codepainters/e800j/docs/scans/cpu800j1.gif

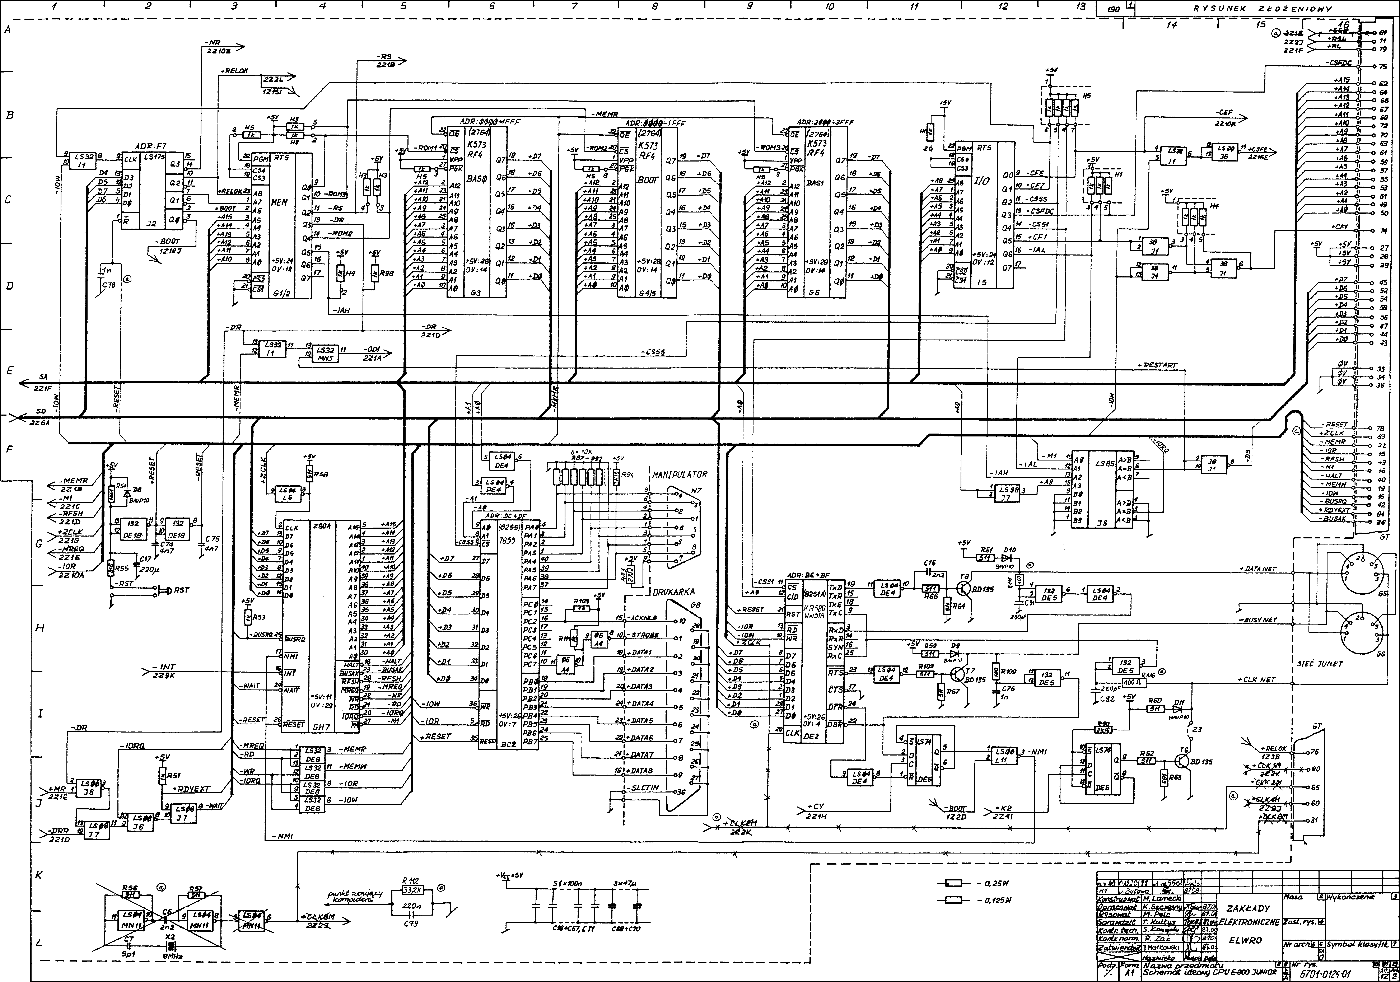
docs/scans/cpu800j1.gif
