codepainters/e800j/docs/scart/1.3_cvbs.jpg

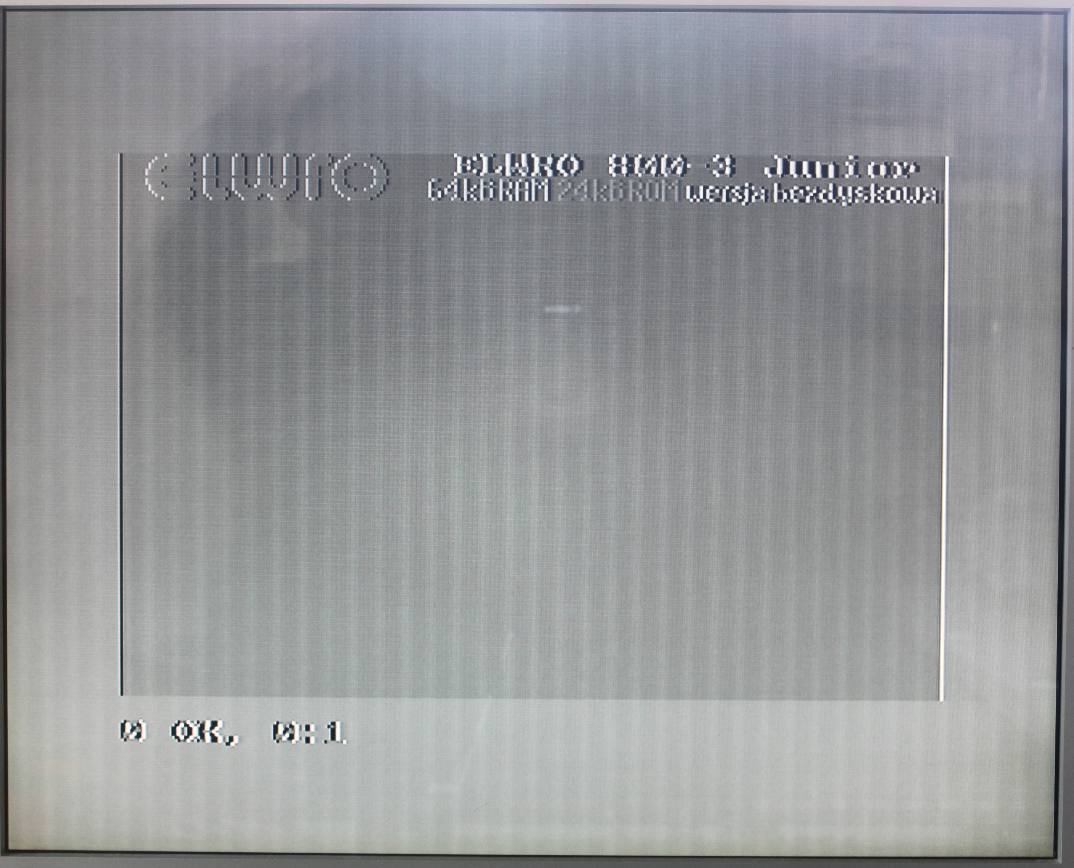
docs/scart/1.3_cvbs.jpg
