codepainters/e800j/docs/scart/scope/p16_b7.png

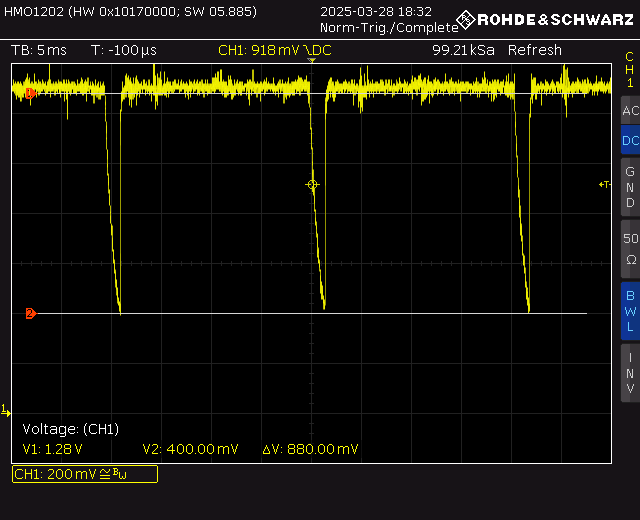
docs/scart/scope/p16_b7.png
