codepainters/e800j/docs/scart/scope/sync_loaded_noise.png

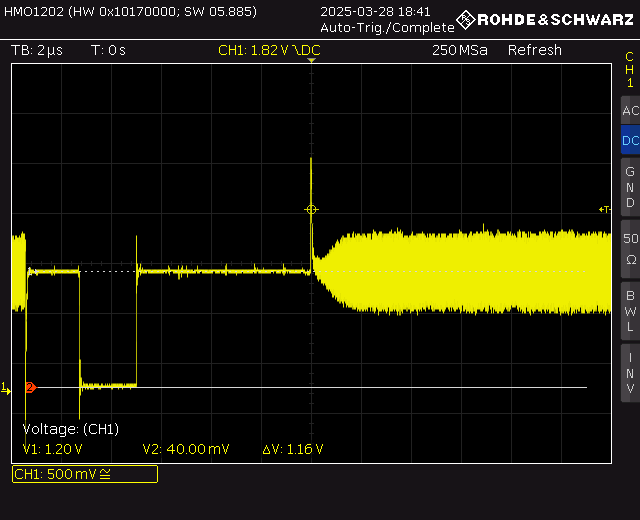
docs/scart/scope/sync_loaded_noise.png
