codepainters/e800j/docs/scart/scope/sync_unloaded.png

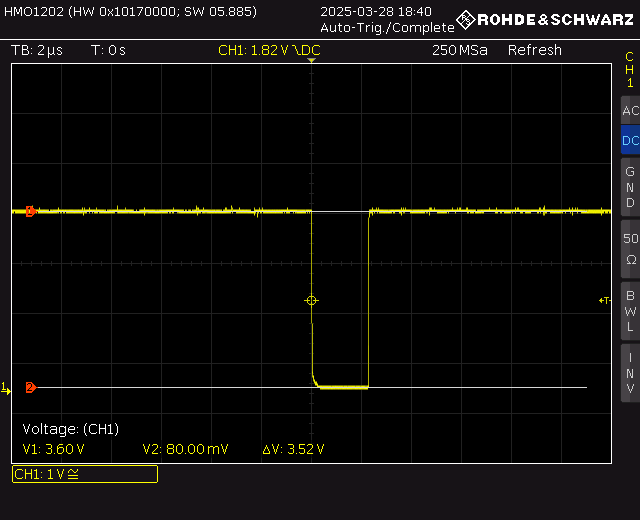
docs/scart/scope/sync_unloaded.png
