codepainters/e800j/kbd_cherry/docs/dtr/20101008153010374_0008.jpg

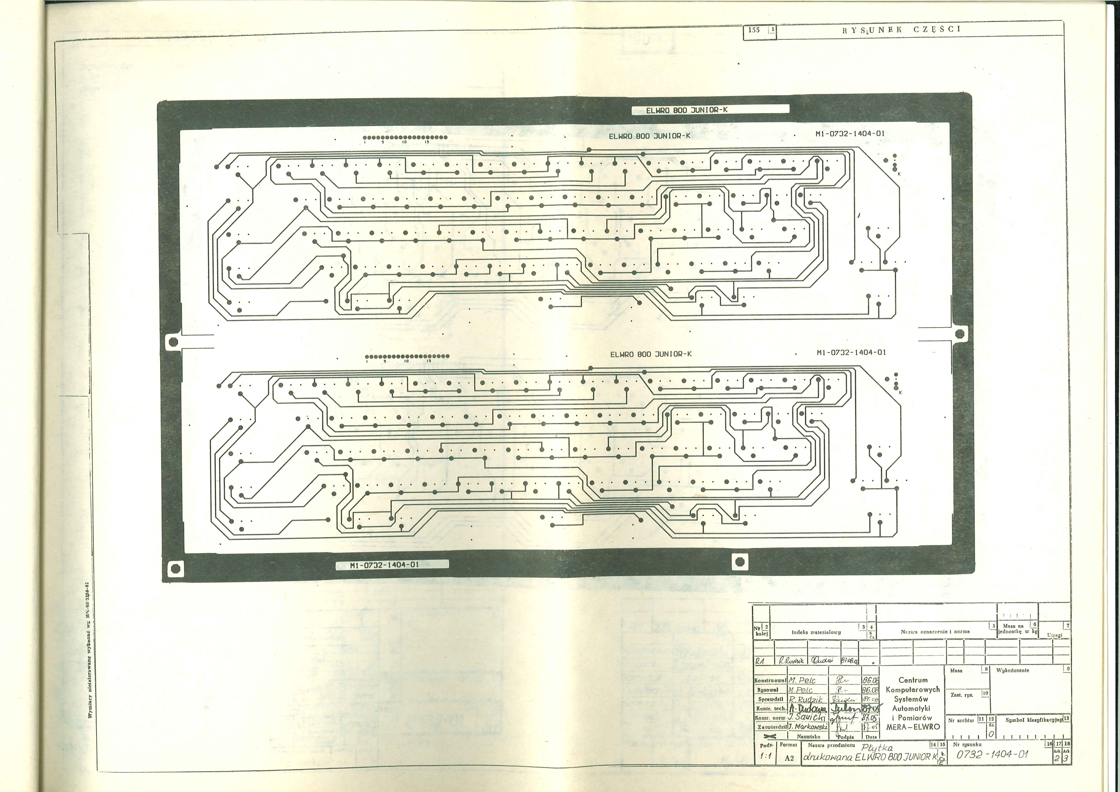
kbd_cherry/docs/dtr/20101008153010374_0008.jpg
