codepainters/e800j/kbd_cherry/docs/dtr/bottom.jpg

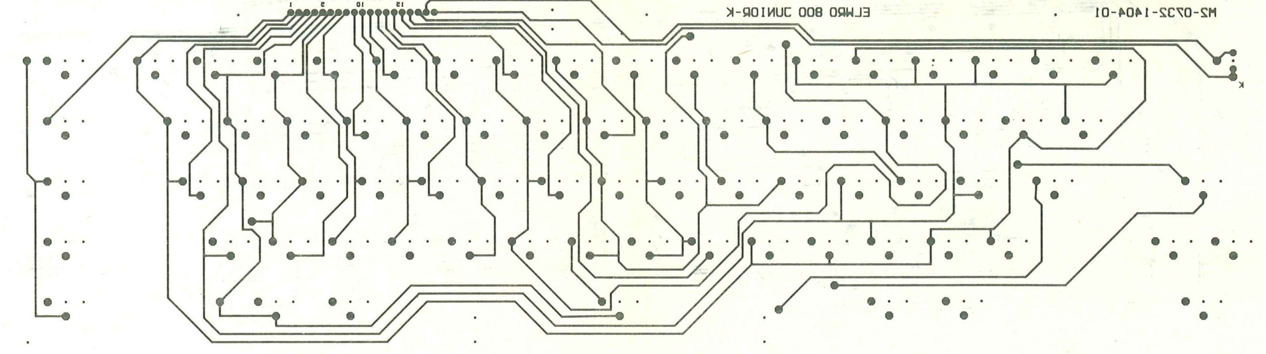
kbd_cherry/docs/dtr/bottom.jpg
