codepainters/e800j/kbd_cherry/docs/dtr/top.jpg

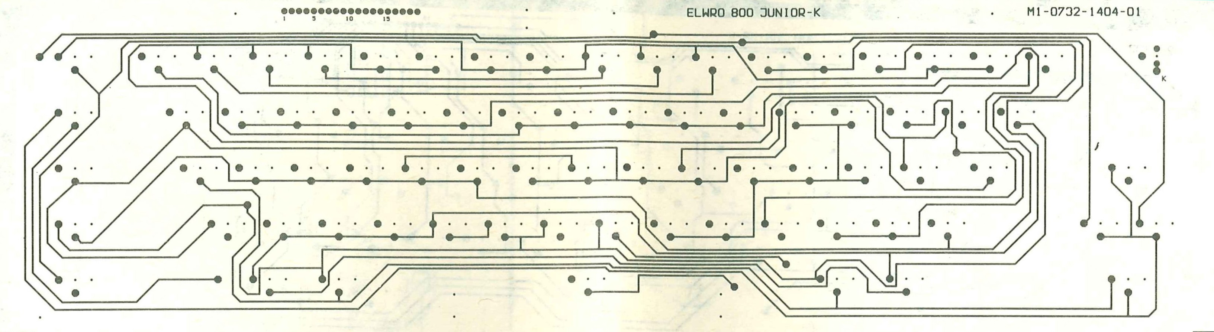
kbd_cherry/docs/dtr/top.jpg
