codepainters/e800j/ports_pcb/3d/DSUB-9_Female_Horizontal_P2.77x2.84mm_EdgePinOffset7.70mm_Housed_MountingHolesOffset9.12mm.step

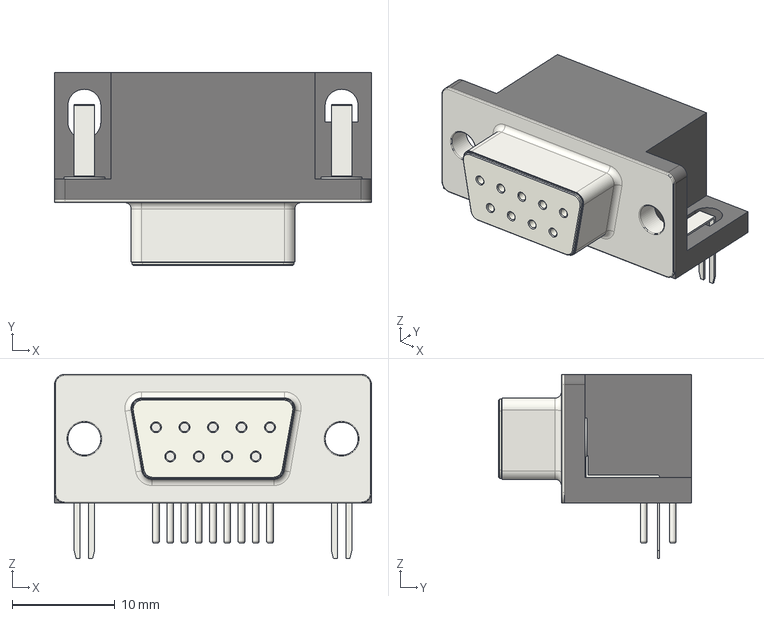
[picture p52: CAD file, 2025-04-09]
ports_pcb/3d/DSUB-9_Female_Horizontal_P2.77x2.84mm_EdgePinOffset7.70mm_Housed_MountingHolesOffset9.12mm.step
30.8 x 18.7 x 17.9 mm
