codepainters/e800j/e800j_rev_c/3d/R_Array_SIP9.step

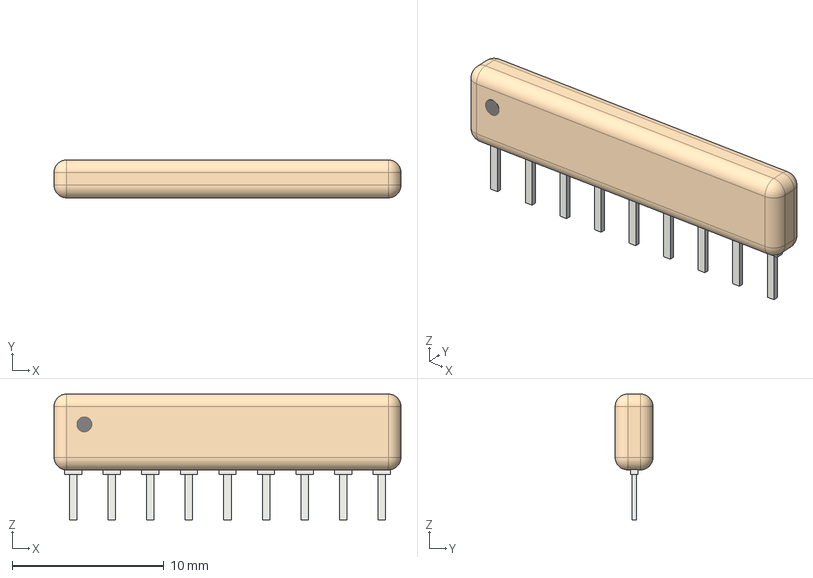
[picture p53: CAD file, 2025-04-16]
e800j_rev_c/3d/R_Array_SIP9.step
22.9 x 2.51 x 8.30 mm
