codepainters/e800j/ports_pcb/3d/PS-22F03.step

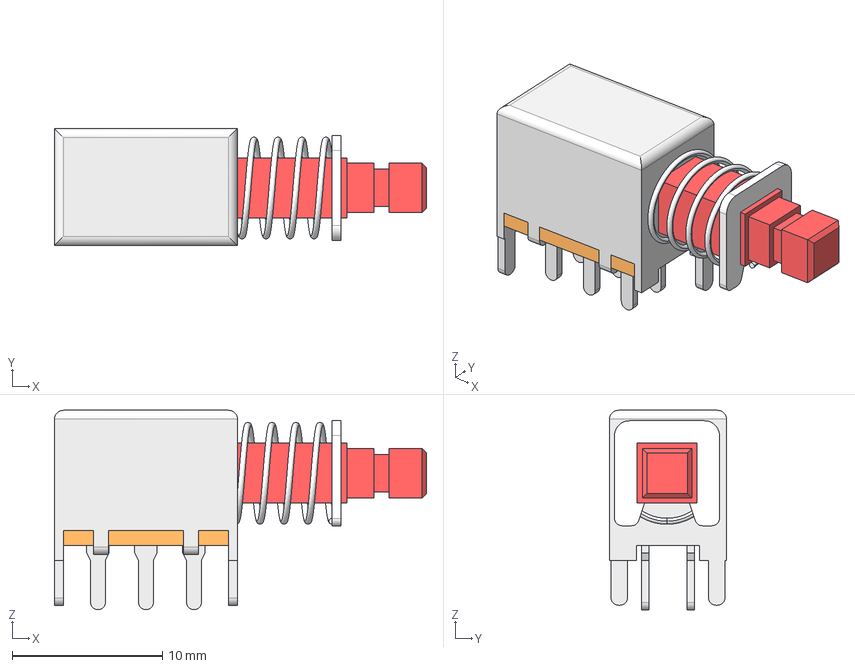
[picture p54: CAD file, 2025-04-07]
ports_pcb/3d/PS-22F03.step
24.8 x 7.80 x 13.3 mm
bottom
pin x 6
Shaft
Locker
Spring
