codepainters/e800j/e800j_rev_c/3d/C_Disc_D3.0mm_W1.6mm_P2.50mm.step

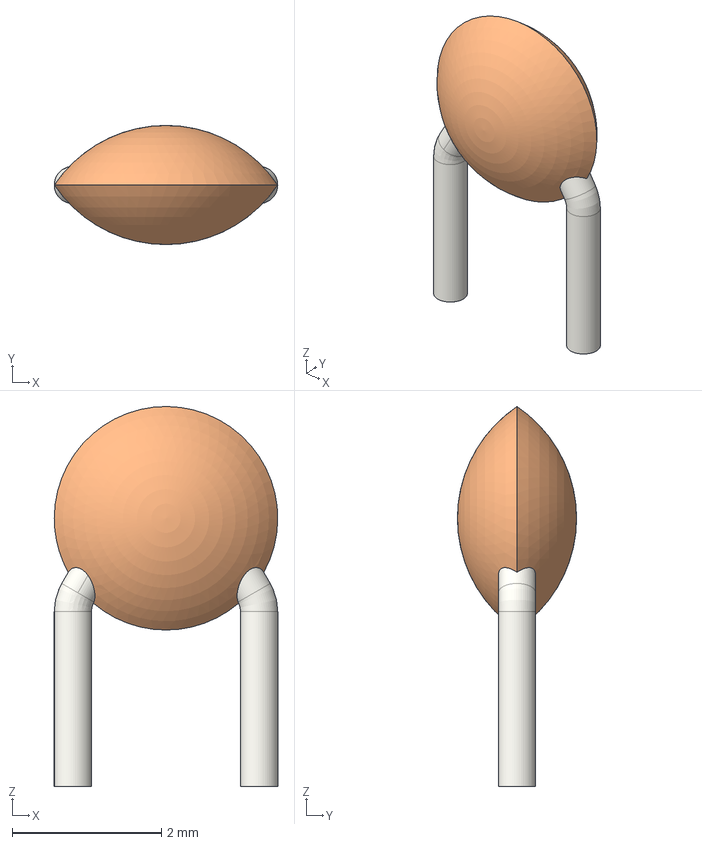
[picture p55: CAD file, 2025-04-16]
e800j_rev_c/3d/C_Disc_D3.0mm_W1.6mm_P2.50mm.step
3.00 x 1.60 x 5.10 mm
