codepainters/e800j/ports_pcb/3d/DCJ200-10-A-K1-K.step

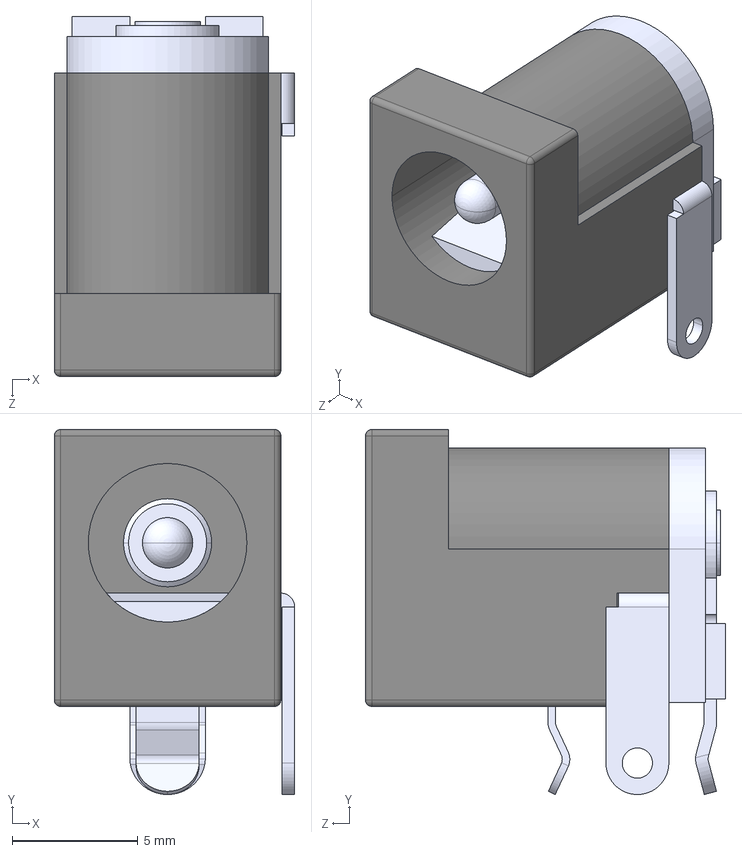
[picture p56: CAD file, 2025-04-07]
ports_pcb/3d/DCJ200-10-A-K1-K.step
9.55 x 14.5 x 14.3 mm
