codepainters/e800j/e800j_rev_c/3d/SW_DIP_SPSTx08_Piano_10.8x21.88mm_W7.62mm_P2.54mm.step

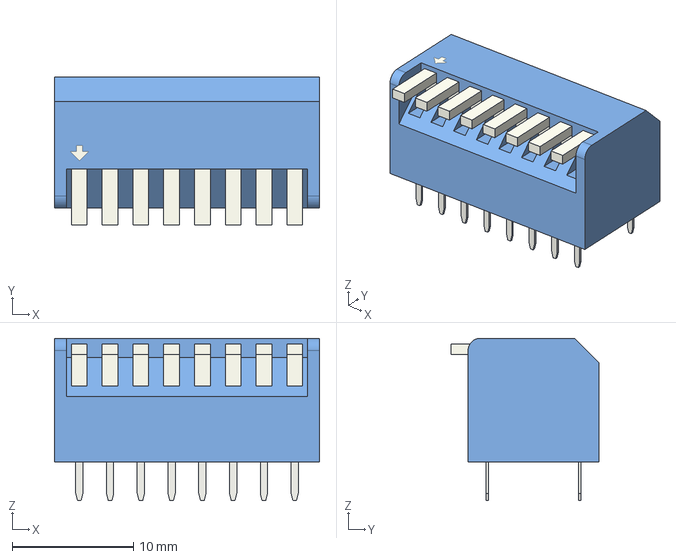
[picture p57: CAD file, 2025-04-16]
e800j_rev_c/3d/SW_DIP_SPSTx08_Piano_10.8x21.88mm_W7.62mm_P2.54mm.step
21.9 x 12.2 x 13.4 mm
