codepainters/e800j/e800j_rev_c/3d/C_Disc_D4.3mm_W1.9mm_P5.00mm.step

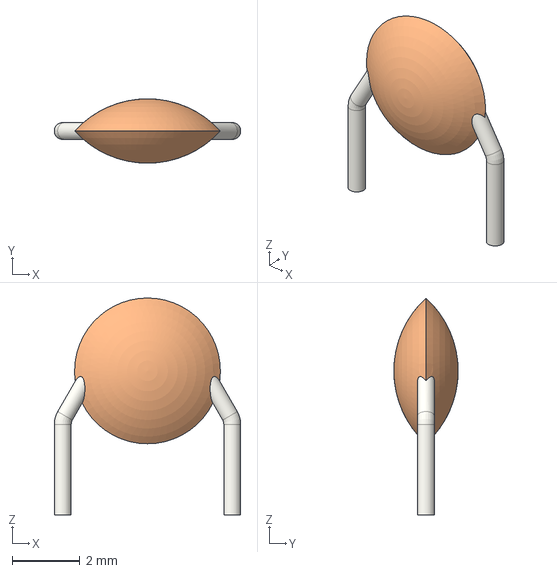
[picture p58: CAD file, 2025-04-16]
e800j_rev_c/3d/C_Disc_D4.3mm_W1.9mm_P5.00mm.step
5.50 x 1.90 x 6.40 mm
