codepainters/e800j/e800j_rev_c/3d/DIP-40_W15.24mm.step

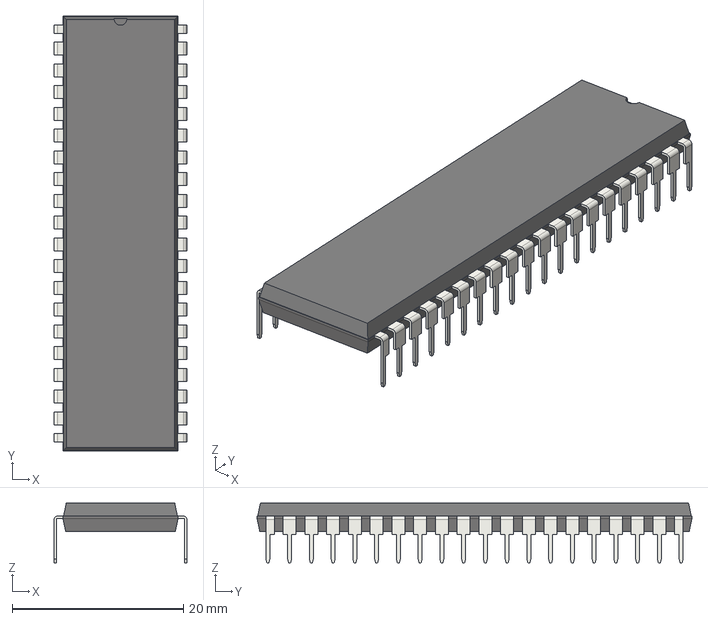
[picture p59: CAD file, 2025-04-16]
e800j_rev_c/3d/DIP-40_W15.24mm.step
15.5 x 50.8 x 6.98 mm
