codepainters/e800j/e800j_rev_c/3d/DIP-16_W7.62mm.step

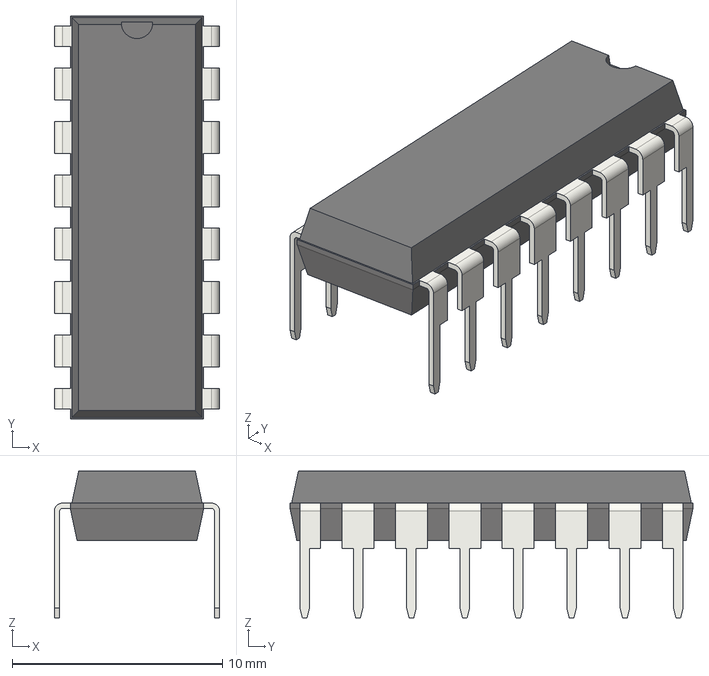
[picture p60: CAD file, 2025-04-16]
e800j_rev_c/3d/DIP-16_W7.62mm.step
7.87 x 19.2 x 6.98 mm
