codepainters/e800j/e800j_rev_c/3d/R_Axial_DIN0309_L9.0mm_D3.2mm_P12.70mm_Horizontal.step

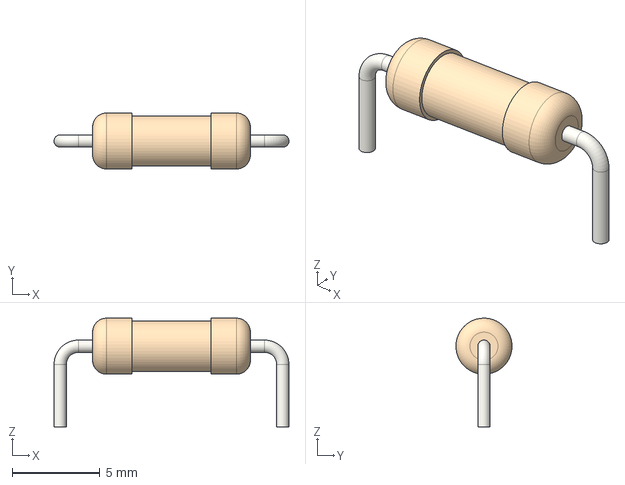
[picture p61: CAD file, 2025-04-16]
e800j_rev_c/3d/R_Axial_DIN0309_L9.0mm_D3.2mm_P12.70mm_Horizontal.step
13.4 x 3.20 x 6.20 mm
