codepainters/e800j/e800j_rev_c/3d/DIP-24_W15.24mm.step

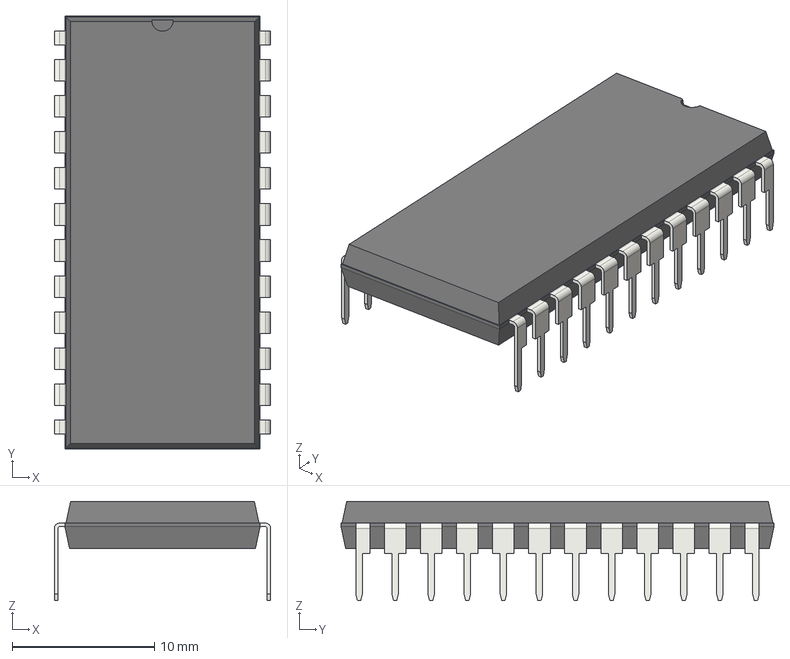
[picture p62: CAD file, 2025-04-16]
e800j_rev_c/3d/DIP-24_W15.24mm.step
15.2 x 30.5 x 6.98 mm
