codepainters/e800j/e800j_rev_c/3d/R_Axial_DIN0204_L3.6mm_D1.6mm_P7.62mm_Horizontal.step

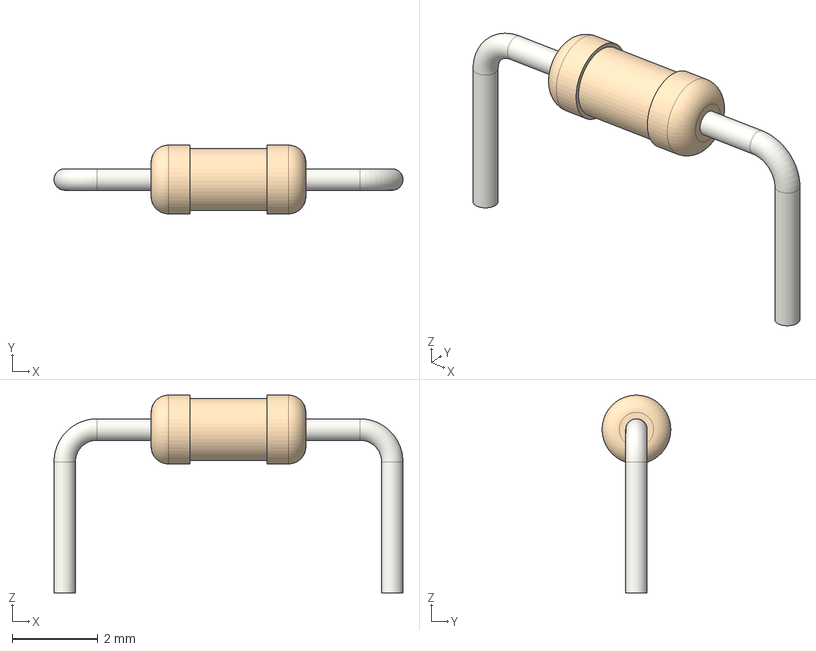
[picture p63: CAD file, 2025-04-16]
e800j_rev_c/3d/R_Axial_DIN0204_L3.6mm_D1.6mm_P7.62mm_Horizontal.step
8.12 x 1.60 x 4.60 mm
