codepainters/e800j/e800j_rev_c/3d/R_Array_SIP5.step

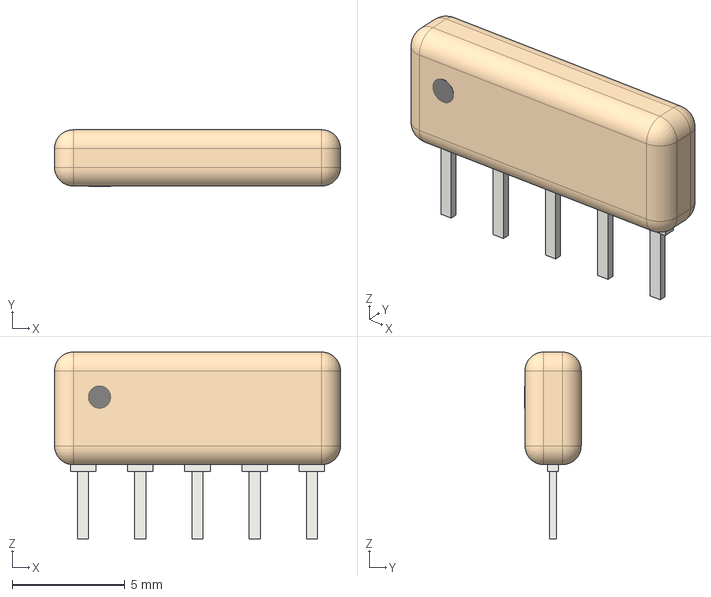
[picture p64: CAD file, 2025-04-16]
e800j_rev_c/3d/R_Array_SIP5.step
12.7 x 2.51 x 8.30 mm
