codepainters/e800j/e800j_rev_c/3d/TO-126-3_Vertical.step

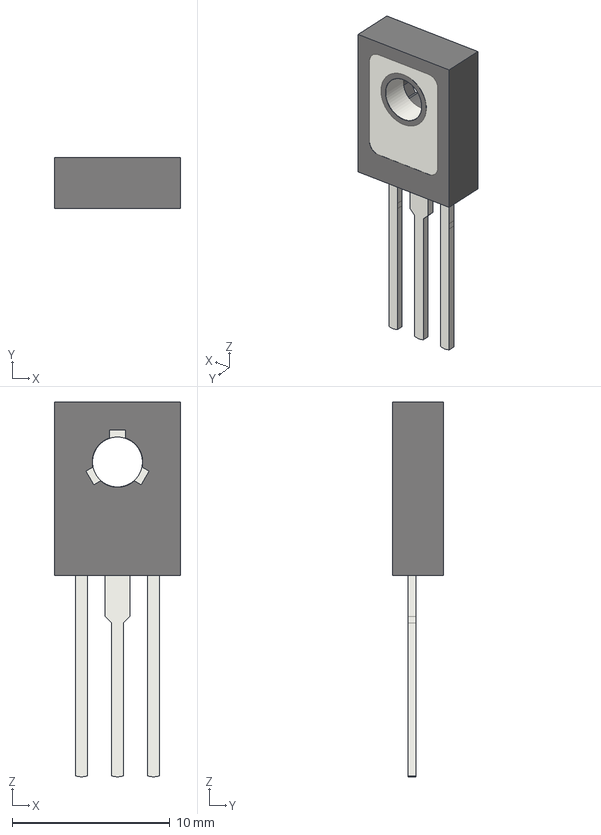
[picture p65: CAD file, 2025-04-16]
e800j_rev_c/3d/TO-126-3_Vertical.step
8.00 x 3.25 x 23.8 mm
