codepainters/e800j/e800j_rev_c/3d/R_Axial_DIN0207_L6.3mm_D2.5mm_P10.16mm_Horizontal.step

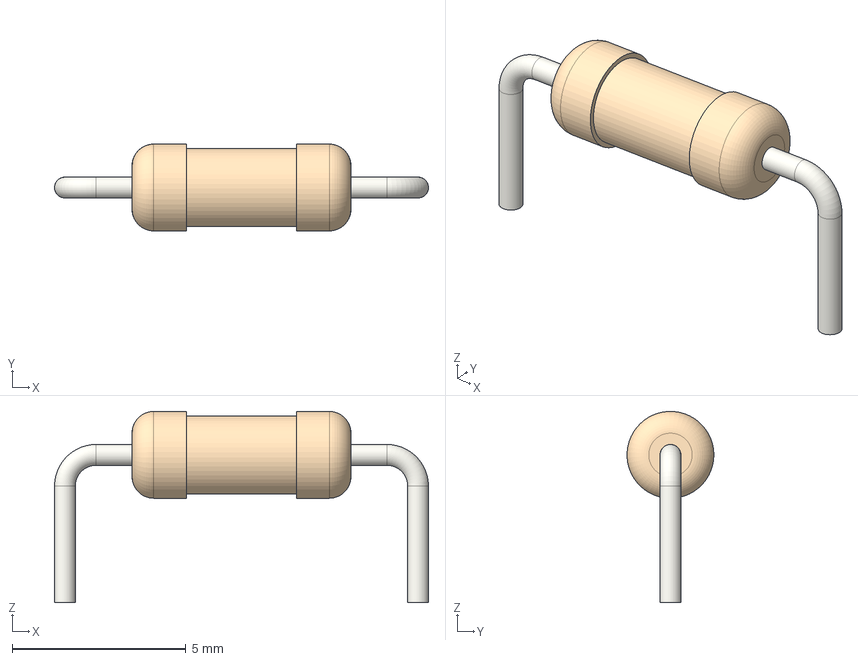
[picture p66: CAD file, 2025-04-16]
e800j_rev_c/3d/R_Axial_DIN0207_L6.3mm_D2.5mm_P10.16mm_Horizontal.step
10.8 x 2.50 x 5.50 mm
