codepainters/e800j/e800j_rev_c/3d/DIP-18_W7.62mm.step

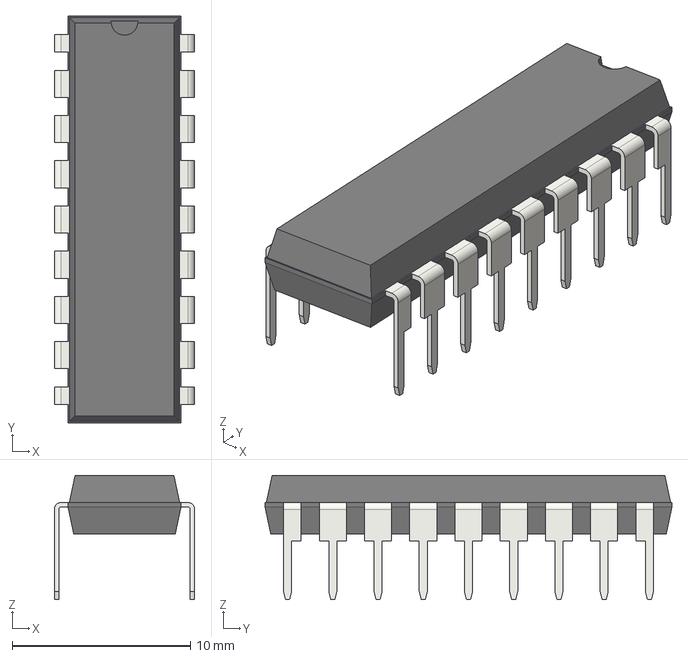
[picture p67: CAD file, 2025-04-16]
e800j_rev_c/3d/DIP-18_W7.62mm.step
7.87 x 22.9 x 6.98 mm
