codepainters/e800j/e800j_rev_c/3d/eltra841.step

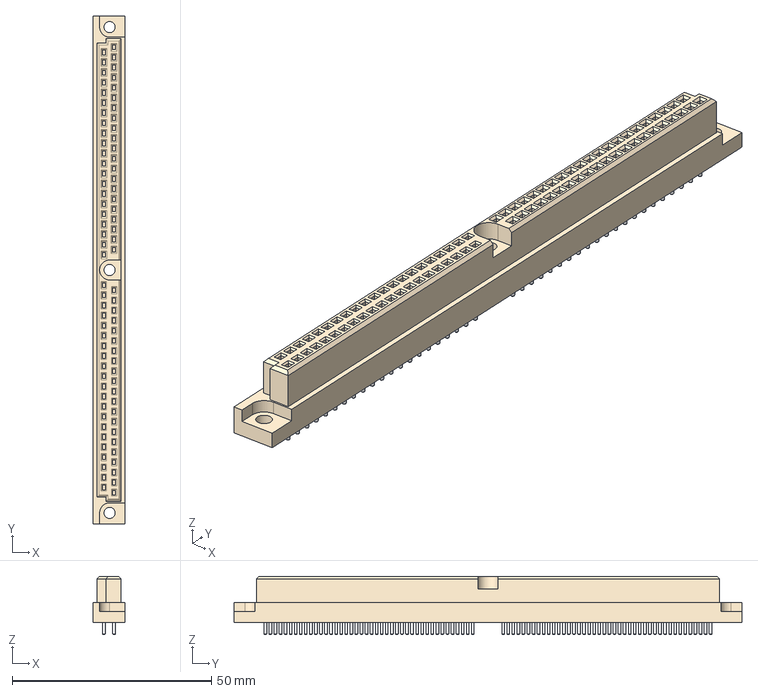
[picture p68: CAD file, 2025-04-07]
e800j_rev_c/3d/eltra841.step
8.10 x 127.5 x 14.6 mm
