codepainters/e800j/e800j_rev_c/3d/gwp10.step

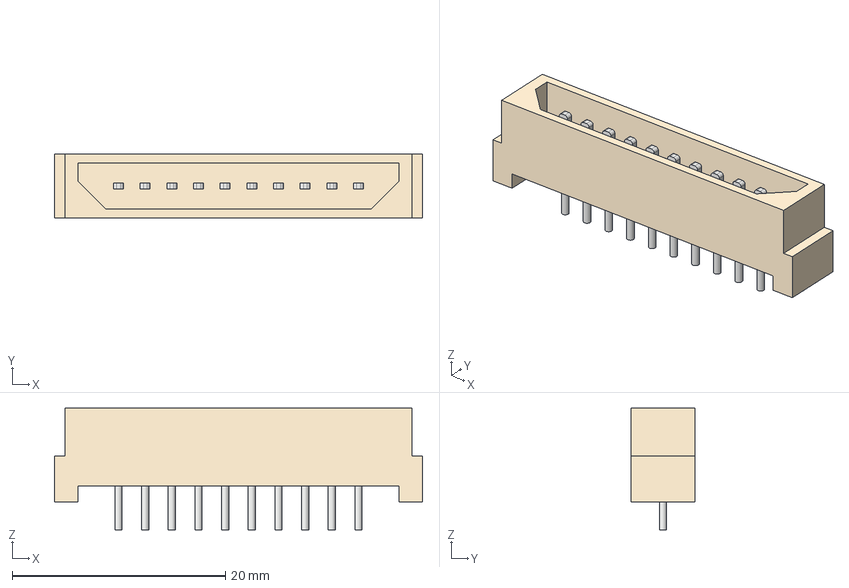
[picture p69: CAD file, 2025-04-07]
e800j_rev_c/3d/gwp10.step
34.5 x 6.00 x 11.4 mm
pins
pins_up
