codepainters/e800j/e800j_rev_c/3d/do-35.stp

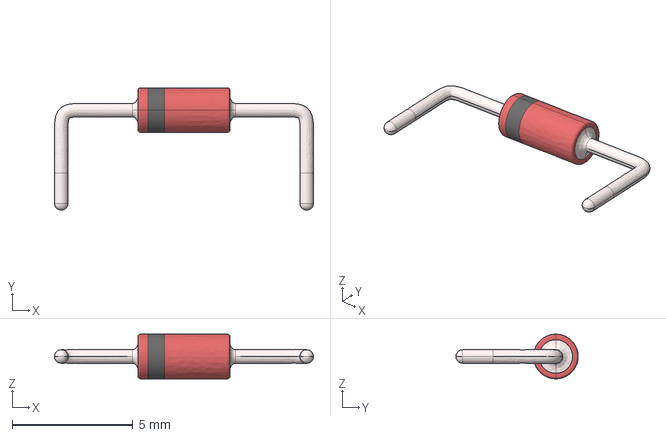
[picture p70: CAD file, 2025-04-07]
e800j_rev_c/3d/do-35.stp
10.7 x 5.07 x 1.85 mm
